LauKH312/Project-Trace/firmware/Project_Trace/Core/Src/bitfont.c

/*
 * bitfont.c
 *
 *  Created on: May 9, 2026
 *      Author: Laurits
 */



/*
    MultilloMono Bitfont
        by Laurits Hillemann
*/

#include <bitfont.h>

const Glyph GLYPHS[94] = {
GLYPH(0x00, 0x00, 0x02, 0x02, 0x02, 0x02, 0x00, 0x02), /* ! */
GLYPH(0x00, 0x00, 0x0a, 0x0a, 0x00, 0x00, 0x00, 0x00), /* " */
GLYPH(0x00, 0x14, 0x14, 0x3e, 0x14, 0x3e, 0x14, 0x14), /* # */
GLYPH(0x04, 0x0e, 0x05, 0x0e, 0x14, 0x15, 0x0e, 0x04), /* $ */
GLYPH(0x00, 0x22, 0x25, 0x15, 0x4a, 0xa8, 0xa4, 0x44), /* % */
GLYPH(0x00, 0x1c, 0x22, 0x12, 0x4c, 0x52, 0x22, 0x5c), /* & */
GLYPH(0x00, 0x00, 0x02, 0x02, 0x00, 0x00, 0x00, 0x00), /* ' */
GLYPH(0x00, 0x40, 0x20, 0x20, 0x20, 0x20, 0x20, 0x40), /* ( */
GLYPH(0x00, 0x02, 0x04, 0x04, 0x04, 0x04, 0x04, 0x02), /* ) */
GLYPH(0x00, 0x00, 0x0a, 0x04, 0x0a, 0x00, 0x00, 0x00), /* * */
GLYPH(0x00, 0x00, 0x08, 0x08, 0x3e, 0x08, 0x08, 0x00), /* + */
GLYPH(0x00, 0x00, 0x00, 0x00, 0x00, 0x00, 0x02, 0x02), /* , */
GLYPH(0x00, 0x00, 0x00, 0x00, 0x7e, 0x00, 0x00, 0x00), /* - */
GLYPH(0x00, 0x00, 0x00, 0x00, 0x00, 0x00, 0x00, 0x02), /* . */
GLYPH(0x00, 0x00, 0x08, 0x08, 0x04, 0x04, 0x02, 0x02), /* / */
GLYPH(0x00, 0x1c, 0x32, 0x2a, 0x2a, 0x2a, 0x26, 0x1c), /* 0 */
GLYPH(0x00, 0x08, 0x0c, 0x08, 0x08, 0x08, 0x08, 0x3e), /* 1 */
GLYPH(0x00, 0x1c, 0x22, 0x20, 0x18, 0x04, 0x02, 0x3e), /* 2 */
GLYPH(0x00, 0x3e, 0x20, 0x20, 0x1c, 0x20, 0x22, 0x1c), /* 3 */
GLYPH(0x00, 0x30, 0x28, 0x24, 0x22, 0x3e, 0x20, 0x20), /* 4 */
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
GLYPH(0x00, 0x00, 0x22, 0x22, 0x1c, 0x22, 0x22, 0x22), /* x */
GLYPH(0x00, 0x00, 0x24, 0x24, 0x38, 0x20, 0x20, 0x1c), /* y */
GLYPH(0x00, 0x00, 0x3e, 0x20, 0x18, 0x04, 0x02, 0x3e), /* z */
GLYPH(0x00, 0x60, 0x10, 0x10, 0x08, 0x10, 0x10, 0x60), /* { */
GLYPH(0x00, 0x10, 0x10, 0x10, 0x10, 0x10, 0x10, 0x10), /* | */
GLYPH(0x00, 0x06, 0x08, 0x08, 0x10, 0x08, 0x08, 0x06), /* } */
GLYPH(0x00, 0x00, 0x00, 0x0c, 0x5a, 0x30, 0x00, 0x00), /* ~ */
};
const Glyph UNKNOWN_CHARACTER = GLYPH(0x7f, 0x41, 0x41, 0x41, 0x41, 0x41, 0x41, 0x7f);

const char BITFONT_MIN_ASCII = 33;
const char BITFONT_MAX_ASCII = 126;

Glyph bitfont_ascii_to_glyph(char ch) {
	if (ch >= BITFONT_MIN_ASCII && ch <= BITFONT_MAX_ASCII) return GLYPHS[ch - BITFONT_MIN_ASCII];
	return UNKNOWN_CHARACTER;
}
