LauKH312/Project-Trace/firmware/Project_Trace/Core/Src/hal_signal_path.c

/*
 * hal_signal_path.c
 *
 *  Created on: 27. apr. 2026
 *      Author: Marius H. Tyson
 */

#include <stm32h7xx_hal.h>
#include <stm32h7xx_hal_conf.h>
#include <hal_signal_path.h>
#include <hal_gpio.h>
#include <menu_system.h>

const GPIO_Pin_t ATTEN_0DB_PIN  = { .bank = GPIOC, .pin = GPIO_PIN_7 };
const GPIO_Pin_t ATTEN_20DB_PIN = { .bank = GPIOB, .pin = GPIO_PIN_13 };
const GPIO_Pin_t ATTEN_40DB_PIN = { .bank = GPIOB, .pin = GPIO_PIN_12 };
const GPIO_Pin_t GAIN_20DB_PIN  = { .bank = GPIOC, .pin = GPIO_PIN_6 };
const GPIO_Pin_t VOLTMETER_NAMP_TOGGLE = { .bank = GPIOB, .pin = GPIO_PIN_15 };// PB15
const GPIO_Pin_t AC_COUPLE_nEN = { .bank = GPIOB, .pin = GPIO_PIN_3 };

// #include "stm32h7xx_hal.h"

void hal_signal_path_init(void){
//    enum SignalPathAtten *selected_atten = get_selected_atten();
//
//    *selected_atten = SignalPathAtten_0db;
//
//    GPIO_InitTypeDef GPIO_InitStruct = {0};
//
//    __HAL_RCC_GPIOB_CLK_ENABLE();
//    __HAL_RCC_GPIOA_CLK_ENABLE();
//    __HAL_RCC_GPIOC_CLK_ENABLE();
//
//    GPIO_InitStruct.Mode  = GPIO_MODE_OUTPUT_PP;
//    GPIO_InitStruct.Pull  = GPIO_NOPULL;
//    GPIO_InitStruct.Speed = GPIO_SPEED_FREQ_LOW;
//    GPIO_InitStruct.Pin = ATTEN_0DB_PIN.pin;
//    HAL_GPIO_Init(ATTEN_0DB_PIN.bank, &GPIO_InitStruct);
//
//    GPIO_InitStruct.Pin = ATTEN_20DB_PIN.pin;
//    HAL_GPIO_Init(ATTEN_20DB_PIN.bank, &GPIO_InitStruct);
//
//    GPIO_InitStruct.Pin = ATTEN_40DB_PIN.pin;
//    HAL_GPIO_Init(ATTEN_40DB_PIN.bank, &GPIO_InitStruct);
//
//    GPIO_InitStruct.Pin = GAIN_20DB_PIN.pin;
//    HAL_GPIO_Init(GAIN_20DB_PIN.bank, &GPIO_InitStruct);

    HAL_GPIO_WritePin(ATTEN_0DB_PIN.bank,  ATTEN_0DB_PIN.pin,  GPIO_PIN_SET);
    HAL_GPIO_WritePin(ATTEN_20DB_PIN.bank, ATTEN_20DB_PIN.pin, GPIO_PIN_SET);
    HAL_GPIO_WritePin(ATTEN_40DB_PIN.bank, ATTEN_40DB_PIN.pin, GPIO_PIN_SET);
    HAL_GPIO_WritePin(GAIN_20DB_PIN.bank, GAIN_20DB_PIN.pin, GPIO_PIN_RESET);

    HAL_GPIO_WritePin(VOLTMETER_NAMP_TOGGLE.bank, VOLTMETER_NAMP_TOGGLE.pin, GPIO_PIN_SET);

    HAL_GPIO_WritePin(AC_COUPLE_nEN.bank, AC_COUPLE_nEN.pin, GPIO_PIN_SET);
}

void hal_signal_path_attenuator_set(enum SignalPathAtten range){
    HAL_GPIO_WritePin(ATTEN_0DB_PIN.bank,  ATTEN_0DB_PIN.pin,  GPIO_PIN_SET);
    HAL_GPIO_WritePin(ATTEN_20DB_PIN.bank, ATTEN_20DB_PIN.pin, GPIO_PIN_SET);
    HAL_GPIO_WritePin(ATTEN_40DB_PIN.bank, ATTEN_40DB_PIN.pin, GPIO_PIN_SET);
    HAL_GPIO_WritePin(GAIN_20DB_PIN.bank,  GAIN_20DB_PIN.pin,  GPIO_PIN_RESET);

    switch (range)
    {
        case SignalPathAtten_0db:
            HAL_GPIO_WritePin(ATTEN_0DB_PIN.bank, ATTEN_0DB_PIN.pin, GPIO_PIN_RESET);
            break;
        case SignalPathAtten_20db:
            HAL_GPIO_WritePin(ATTEN_20DB_PIN.bank, ATTEN_20DB_PIN.pin, GPIO_PIN_RESET);
            break;
        case SignalPathAtten_40db:
            HAL_GPIO_WritePin(ATTEN_40DB_PIN.bank, ATTEN_40DB_PIN.pin, GPIO_PIN_RESET);
            break;
        default:
            __builtin_unreachable();
            break;
    }
}


void hal_signal_path_accouple_en(_Bool use_accouple) {
    HAL_GPIO_WritePin(AC_COUPLE_nEN.bank, AC_COUPLE_nEN.pin, (use_accouple) ? GPIO_PIN_RESET : GPIO_PIN_SET);
}

// void hal_signal_path_gain_init(void){
//      GPIO_InitTypeDef GPIO_InitStruct = {0};
//      __HAL_RCC_GPIOC_CLK_ENABLE();
//     GPIO_InitStruct.Mode  = GPIO_MODE_OUTPUT_PP;
//     GPIO_InitStruct.Pull  = GPIO_NOPULL;
//     GPIO_InitStruct.Speed = GPIO_SPEED_FREQ_LOW;
//     GPIO_InitStruct.Pin = GAIN_20DB_PIN.pin;
//     HAL_GPIO_Init(GAIN_20DB_PIN.bank, &GPIO_InitStruct);
//     HAL_GPIO_WritePin(GAIN_20DB_PIN.bank,  GAIN_20DB_PIN.pin,  GPIO_PIN_RESET);
// }

// void hal_signal_path_gain_set(enum SignalPathGain range){
//      HAL_GPIO_WritePin(GAIN_20DB_PIN.bank,  GAIN_20DB_PIN.pin,  GPIO_PIN_RESET);
//      switch(range){
//      case SignalPathGain_0db: HAL_GPIO_WritePin(GAIN_20DB_PIN.bank,  GAIN_20DB_PIN.pin,  GPIO_PIN_RESET);  break;
//      case SignalPathGain_20db:
//              HAL_GPIO_WritePin(GAIN_20DB_PIN.bank,  GAIN_20DB_PIN.pin,  GPIO_PIN_SET); break;
//      default:
//              break;
//      }
// }
