LauKH312/Project-Trace/firmware/Project_Trace/Core/Inc/hal_signal_path.h

/*
 * hal_signal_path.h
 *
 *  Created on: 27. apr. 2026
 *      Author: Marius H. Tyson
 */

#ifndef INC_HAL_SIGNAL_PATH_H_
#define INC_HAL_SIGNAL_PATH_H_


#include <stm32h7xx_hal.h>
#include <stm32h7xx_hal_conf.h>
#include <hal_gpio.h>

enum SignalPathAtten {
        SignalPathAtten_0db = 0,
        SignalPathAtten_20db,
        SignalPathAtten_40db
};

void hal_signal_path_init(void);

// enum SignalPathAtten {
//      SignalPathAtten_0db =  0,
//      SignalPathAtten_20db,
//      SignalPathAtten_40db
// };

// enum SignalPathGain {
//      SignalPathGain_0db = 0,
//      SignalPathGain_20db
// };

void hal_signal_path_attenuator_set(enum SignalPathAtten range);
void hal_signal_path_accouple_en(_Bool use_accouple);
// void hal_signal_path_gain_set(enum SignalPathGain range);



#endif /* INC_HAL_SIGNAL_PATH_H_ */
