LauKH312/Project-Trace/firmware/Project_Trace/Core/Src/meas.c

/*
 * meas.c
 *
 *  Created on: May 4, 2026
 *      Author: Laurits
 */


#include <meas.h>

fix9_23 meas_average(const fix9_23* buf, size_t buffer_length) {
    int64_t acc = 0;
    for (size_t i = 0; i < buffer_length; i++) {
        const fix9_23 x = buf[i];
        acc += x.raw;
    } 
    acc /= (int64_t) buffer_length;
    return FIX9_23_RAW((int32_t) acc);
}

fix9_23 meas_rms(const fix9_23* buf, size_t buffer_length) {
    int64_t acc = 0;
    for (size_t i = 0; i < buffer_length; i++) {
        const fix9_23 x = buf[i];
        const int64_t term = (int64_t)x.raw * (int64_t)x.raw;
        acc += term / (1 << FIX9_23_DEC_BITS);
    }

    acc /= buffer_length;
    return fix9_23_sqrt(FIX9_23_RAW((int32_t) acc));
}

fix9_23 meas_max(const fix9_23* buf, size_t buffer_length) {
    fix9_23 max = FIX9_23_RAW(INT32_MIN);

    for (size_t i = 0; i < buffer_length; i++) {
        const fix9_23 x = buf[i];
        if (x.raw > max.raw) max = x;
    }

    return max;

}

fix9_23 meas_min(const fix9_23* buf, size_t buffer_length) {
    fix9_23 min = FIX9_23_RAW(INT32_MAX);

    for (size_t i = 0; i < buffer_length; i++) {
        const fix9_23 x = buf[i];
        if (x.raw > min.raw) min = x;
    }

    return min;
}

_Bool meas_rising_edge(const fix9_23* buf, size_t buffer_length, fix9_23 threshold, size_t* rising_edge_idx) {
	_Bool previous_below_thr = 0;
	for (size_t i = 0; i < buffer_length; i++) {

		if (buf[i].raw > threshold.raw && previous_below_thr) {
			*rising_edge_idx = i;
			return 1;
		}

		previous_below_thr = buf[i].raw < threshold.raw;
	}
	return 0;
}
