LauKH312/Project-Trace/firmware/Project_Trace/Core/Inc/mathdefs.h

/*
 * mathdefs.h
 *
 *  Created on: Jun 9, 2026
 *      Author: Laurits
 */

#ifndef INC_MATHDEFS_H_
#define INC_MATHDEFS_H_

#define MAX(a,b) ((a) > (b) ? (a) : (b))
#define MIN(a,b) ((a) < (b) ? (a) : (b))

#endif /* INC_MATHDEFS_H_ */
